VelcroIsYummy/Bioreactor/Schematic/Bioreactor.kicad_sch

## KiCad design Schematic/Bioreactor.kicad_sch (2026-06-01)

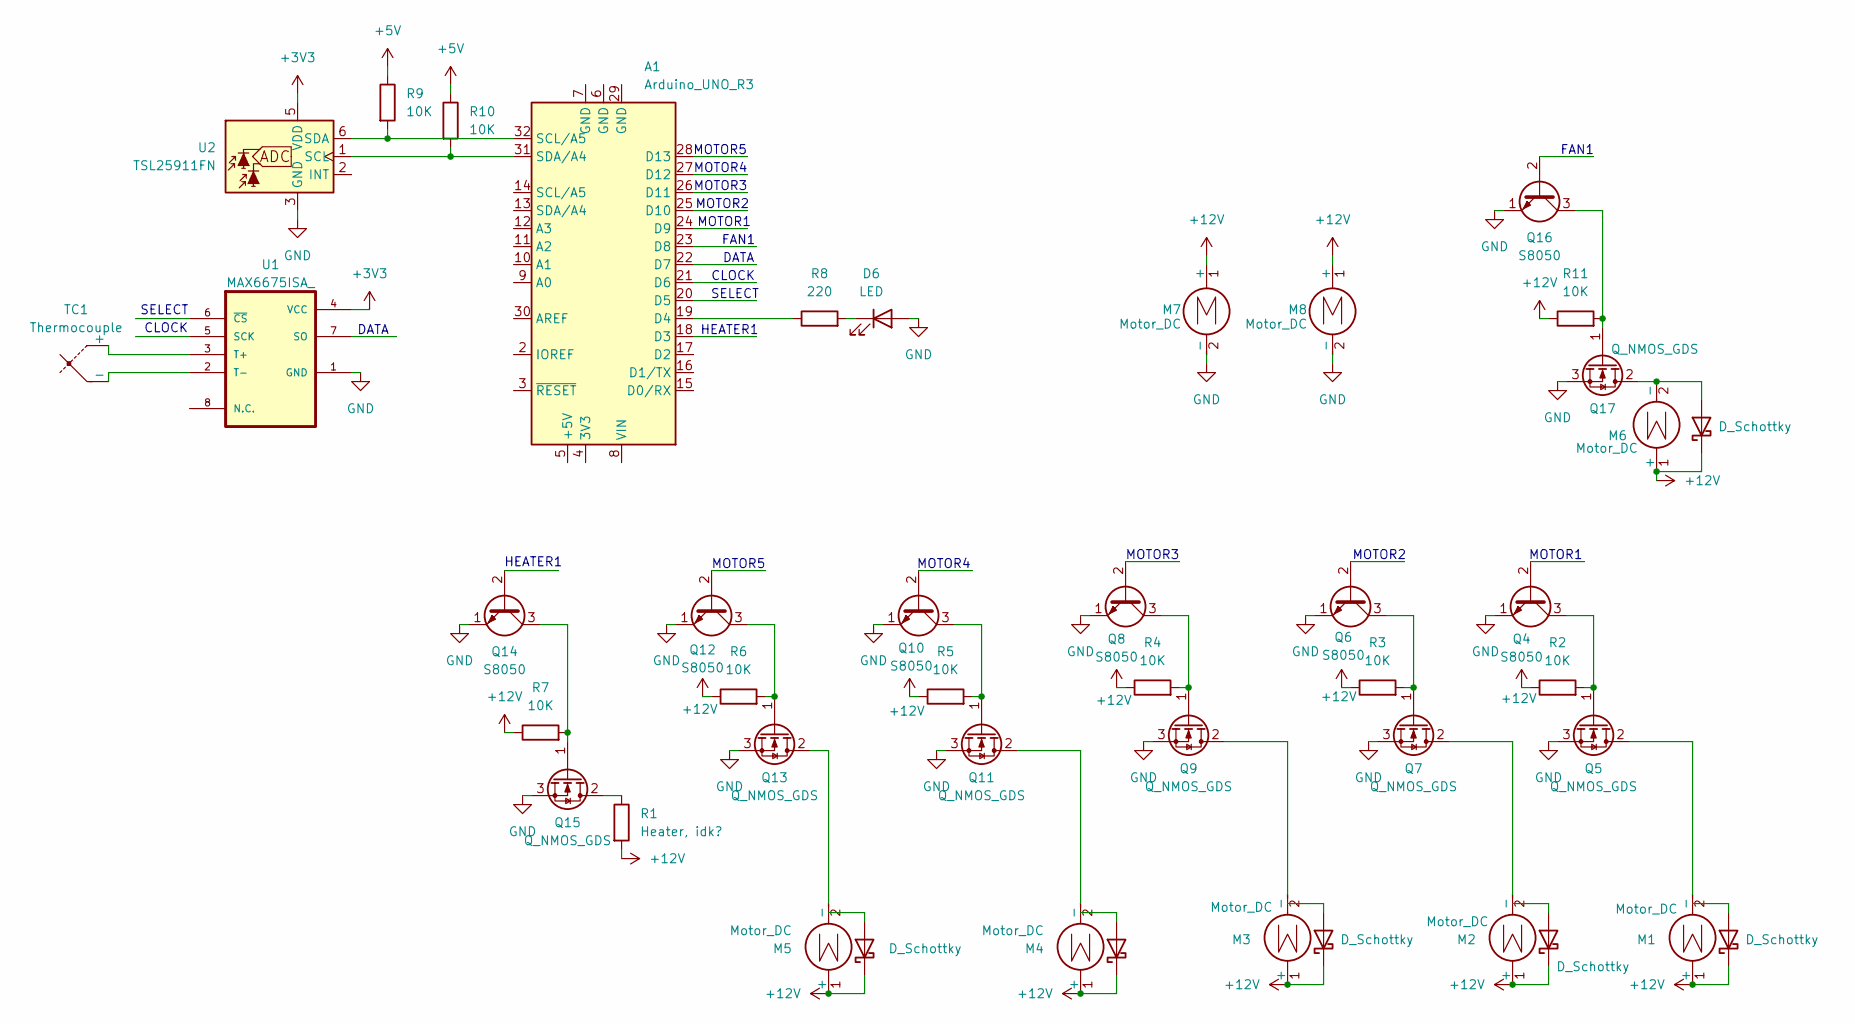
[picture p15: schematic Bioreactor.kicad_sch]

Parts:
A1: Arduino_UNO_R3
D1, D2, D3, D4, D5, D7: D_Schottky
D6: LED
M1, M2, M3, M4, M5, M6, M7, M8: Motor_DC
Q4, Q6, Q8, Q10, Q12, Q14, Q16: S8050; TO-92_Inline
Q5, Q7, Q9, Q11, Q13, Q15, Q17: Q_NMOS_GDS
R1: Heater, idk?
R2, R3, R4, R5, R6, R7, R9, R10, R11: 10K
R8: 220
TC1: Thermocouple
U1: MAX6675ISA_; SOIC127P600X175-8N
U2: TSL25911FN; AMS_TSL25911FN

Connections:
+3V3: U1.4 (VCC), U2.5 (VDD)
+5V: R9.1, R10.1
+12V: D1.1 (K), D2.1 (K), D3.1 (K), D4.1 (K), D5.1 (K), D7.1 (K), M1.1 (+), M2.1 (+), M3.1 (+), M4.1 (+), M5.1 (+), M6.1 (+), M7.1 (+), M8.1 (+), R1.2, R2.1, R3.1, R4.1, R5.1, R6.1, R7.1, R11.1
GND: D6.2 (A), M7.2 (-), M8.2 (-), Q4.1 (E), Q5.3 (S), Q6.1 (E), Q7.3 (S), Q8.1 (E), Q9.3 (S), Q10.1 (E), Q11.3 (S), Q12.1 (E), Q13.3 (S), Q14.1 (E), Q15.3 (S), Q16.1 (E), Q17.3 (S), U1.1 (GND), U2.3 (GND)
unnamed: A1.19 (D4), R8.1
unnamed: A1.31 (SDA/A4), R10.2, U2.1 (SCL)
unnamed: A1.32 (SCL/A5), R9.2, U2.6 (SDA)
unnamed: D6.1 (K), R8.2
unnamed: D7.2 (A), M6.2 (-), Q17.2 (D)
unnamed: M1.2 (-), Q5.2 (D)
unnamed: M2.2 (-), Q7.2 (D)
unnamed: M3.2 (-), Q9.2 (D)
unnamed: M4.2 (-), Q11.2 (D)
unnamed: M5.2 (-), Q13.2 (D)
unnamed: Q4.3 (C), Q5.1 (G), R2.2
unnamed: Q6.3 (C), Q7.1 (G), R3.2
unnamed: Q8.3 (C), Q9.1 (G), R4.2
unnamed: Q10.3 (C), Q11.1 (G), R5.2
unnamed: Q12.3 (C), Q13.1 (G), R6.2
unnamed: Q14.3 (C), Q15.1 (G), R7.2
unnamed: Q15.2 (D), R1.1
unnamed: Q16.3 (C), Q17.1 (G), R11.2
unnamed: TC1.1 (+), U1.3 (T+)
unnamed: TC1.2 (-), U1.2 (T-)

Notes on the sheet:
CLOCK
SELECT
MOTOR1
HEATER1
DATA
MOTOR3
MOTOR5
MOTOR4
FAN1
MOTOR2
